wrhlearner/PacBot-2023/Docs/Hardware/components/motor driver/drv8835 schematic.png

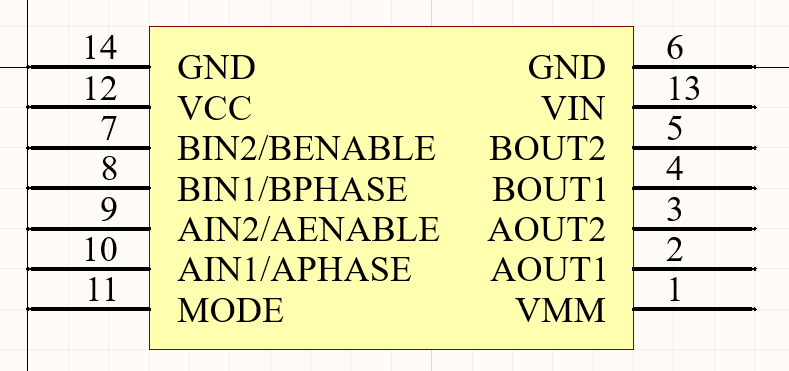
Docs/Hardware/components/motor driver/drv8835 schematic.png
