wrhlearner/PacBot-2023/Docs/Hardware/components/Teensy40/mechanical dimensions front side.png

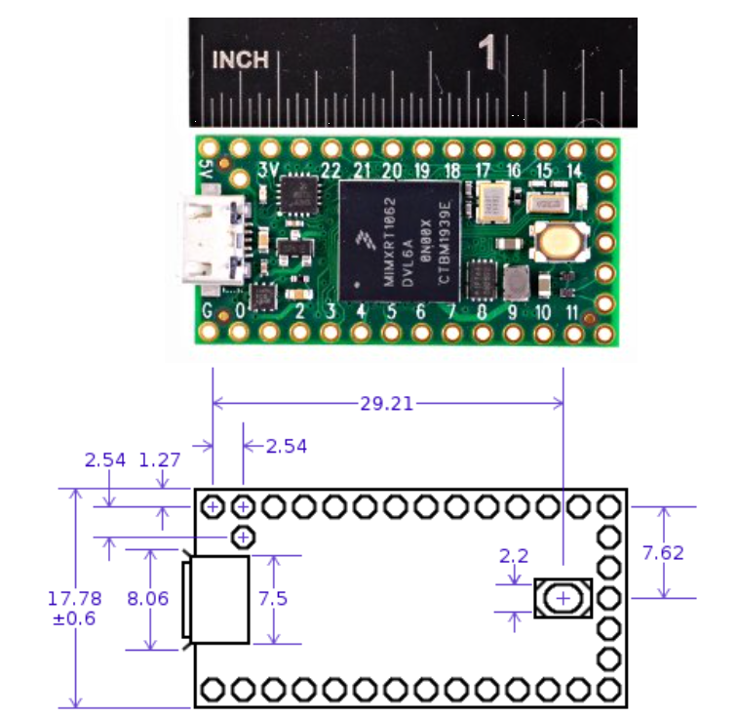
Docs/Hardware/components/Teensy40/mechanical dimensions front side.png
