wrhlearner/PacBot-2023/Docs/Hardware/PCB/3D model back.png

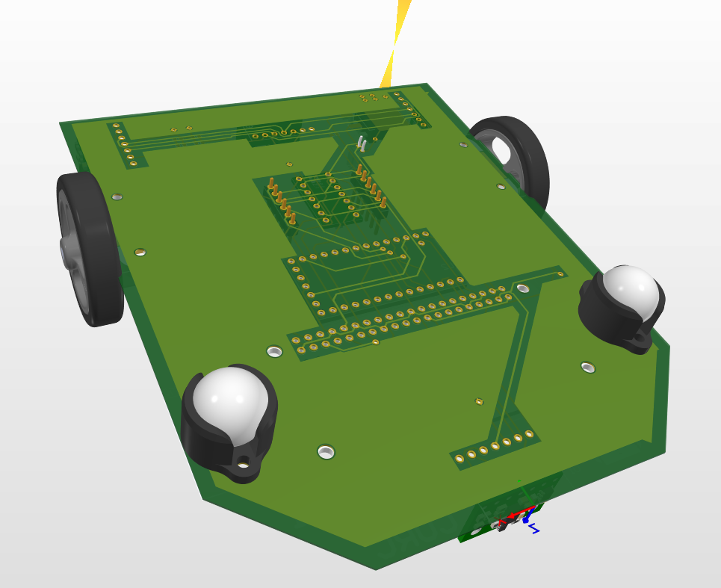
Docs/Hardware/PCB/3D model back.png
