wrhlearner/PacBot-2023/Docs/Hardware/components/magnetic encoder/PCB dimensions.jpg

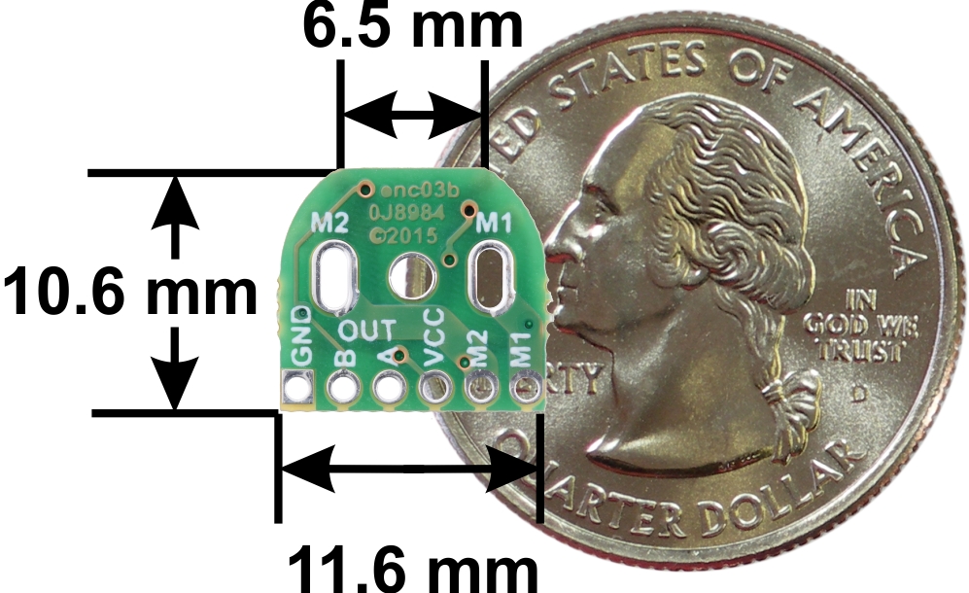
Docs/Hardware/components/magnetic encoder/PCB dimensions.jpg
