wrhlearner/PacBot-2023/Docs/Hardware/components/motor/mounting bracket back.jpg

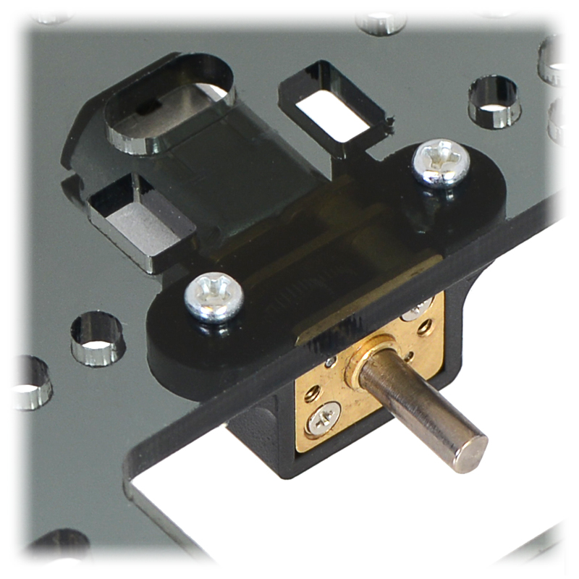
Docs/Hardware/components/motor/mounting bracket back.jpg
