wrhlearner/PacBot-2023/Docs/Hardware/components/Teensy40/Teensy_4.0/Teensy_4.0_PCB.SLDPRT

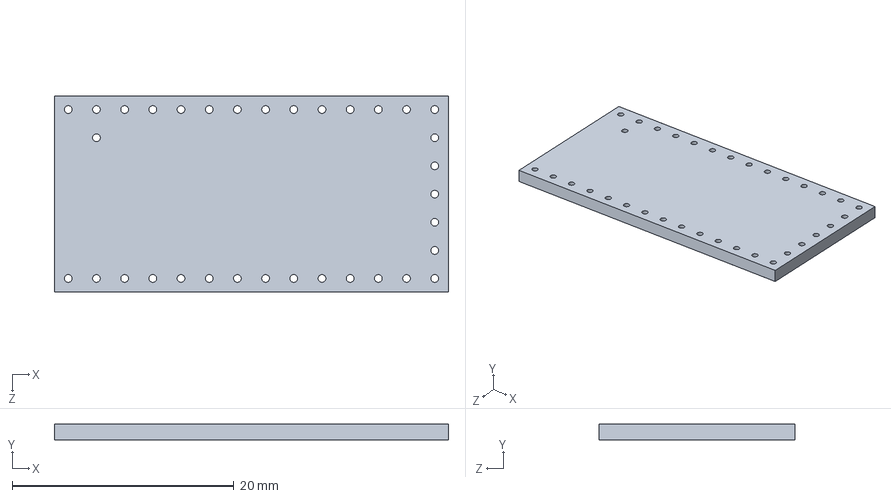
[picture p24: CAD file, 2023-03-19]
Docs/Hardware/components/Teensy40/Teensy_4.0/Teensy_4.0_PCB.SLDPRT
35.5 x 1.40 x 17.7 mm
