wrhlearner/PacBot-2023/Docs/Hardware/components/Teensy40/Teensy_4.0/SKRPACE010 v4.SLDPRT

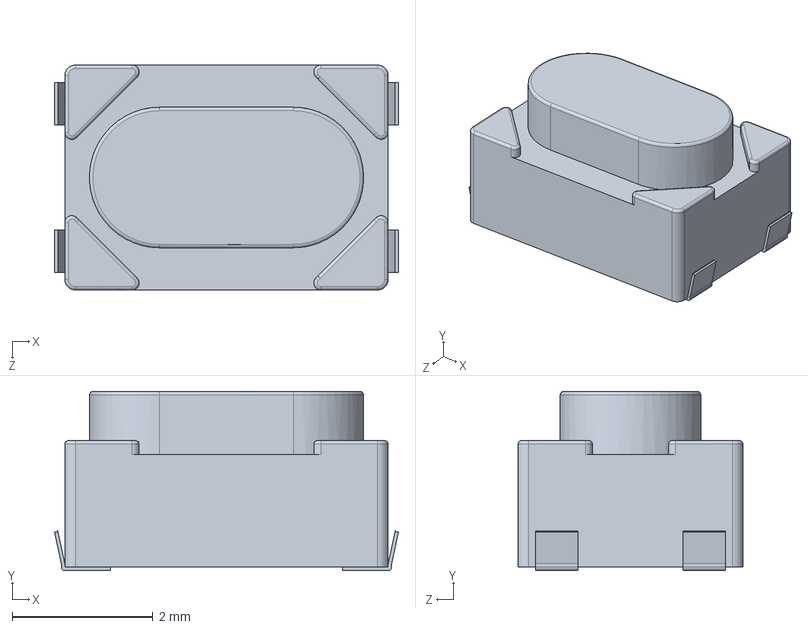
[picture p25: CAD file, 2023-03-19]
Docs/Hardware/components/Teensy40/Teensy_4.0/SKRPACE010 v4.SLDPRT
4.89 x 2.55 x 3.20 mm
