wrhlearner/PacBot-2023/Docs/Hardware/components/magnetic encoder/61300611121_Download_STP_61300611121_rev1.stp

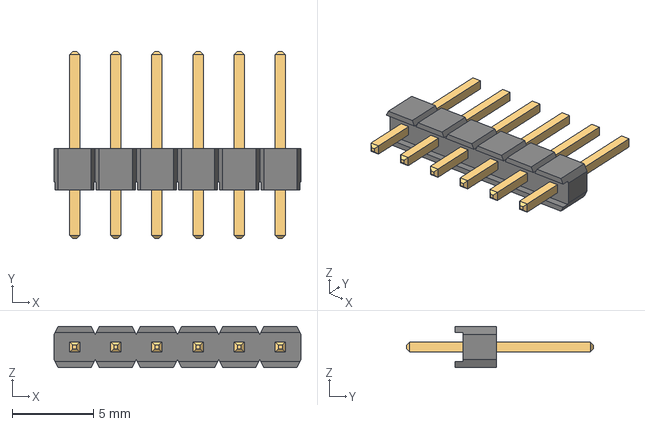
[picture p26: CAD file, 2023-03-19]
Docs/Hardware/components/magnetic encoder/61300611121_Download_STP_61300611121_rev1.stp
15.2 x 11.5 x 2.54 mm
6130xx11121_PIN x 6
