wrhlearner/PacBot-2023/Docs/Hardware/components/magnetic encoder/soldering 0.1'' male headers.jpg

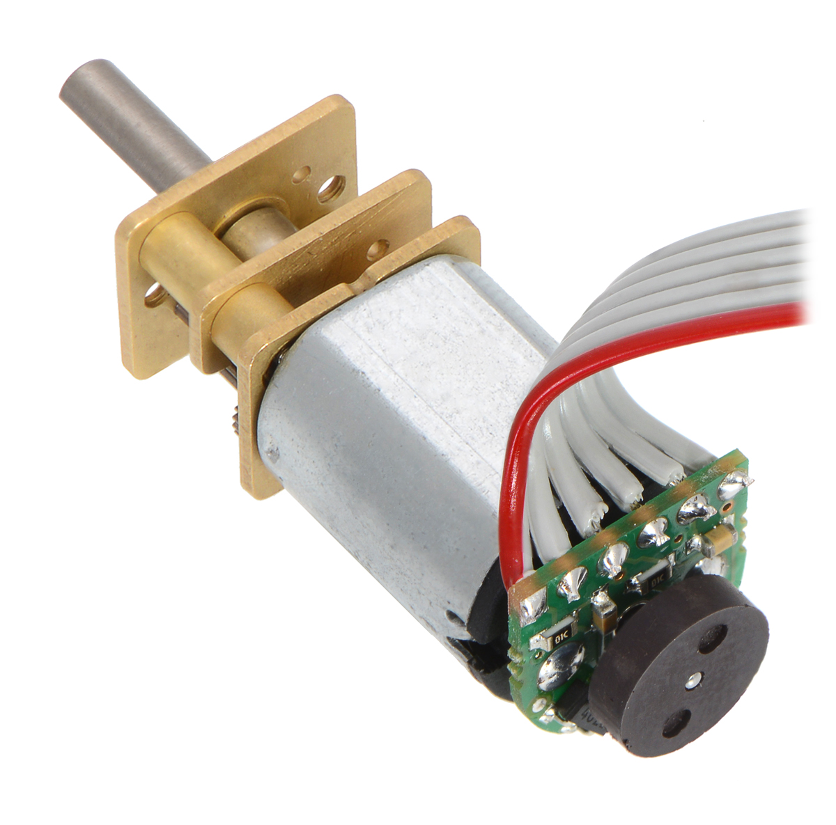
Docs/Hardware/components/magnetic encoder/soldering 0.1'' male headers.jpg
