wrhlearner/PacBot-2023/Docs/Hardware/components/RPY/2x20 GPIO header.pdf

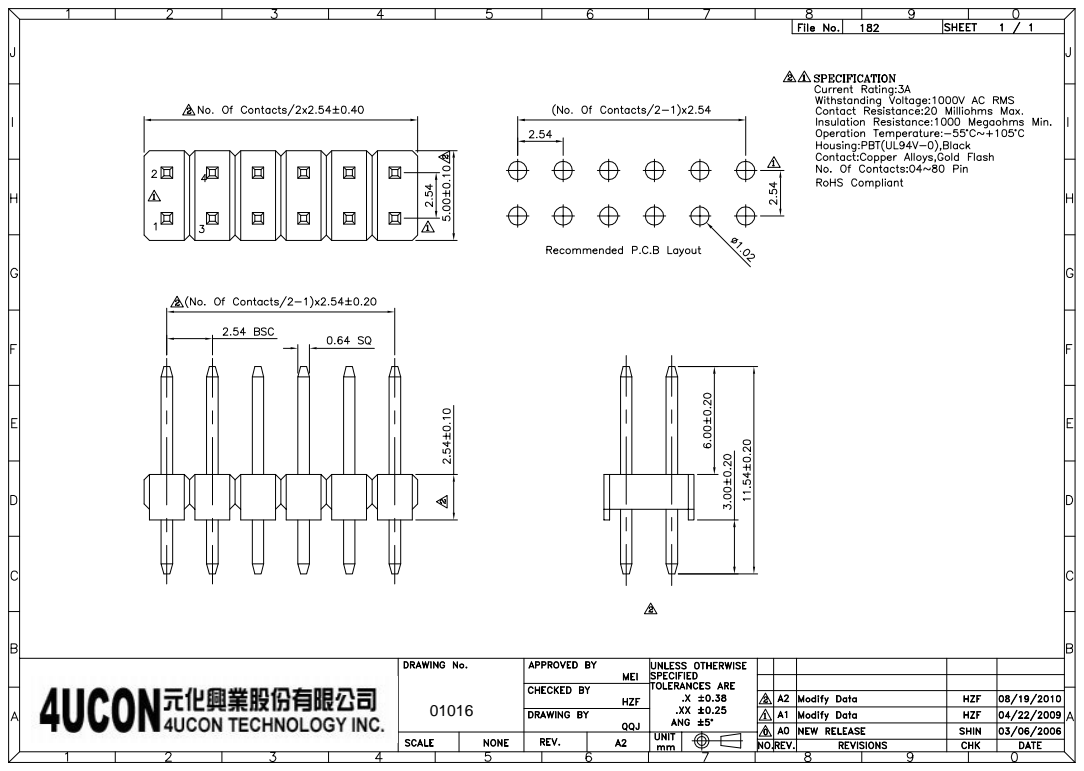
[picture p31: page 1]
