wrhlearner/PacBot-2023/Docs/Hardware/components/RPY/C4114.CP25412-40G-S116-A.pdf

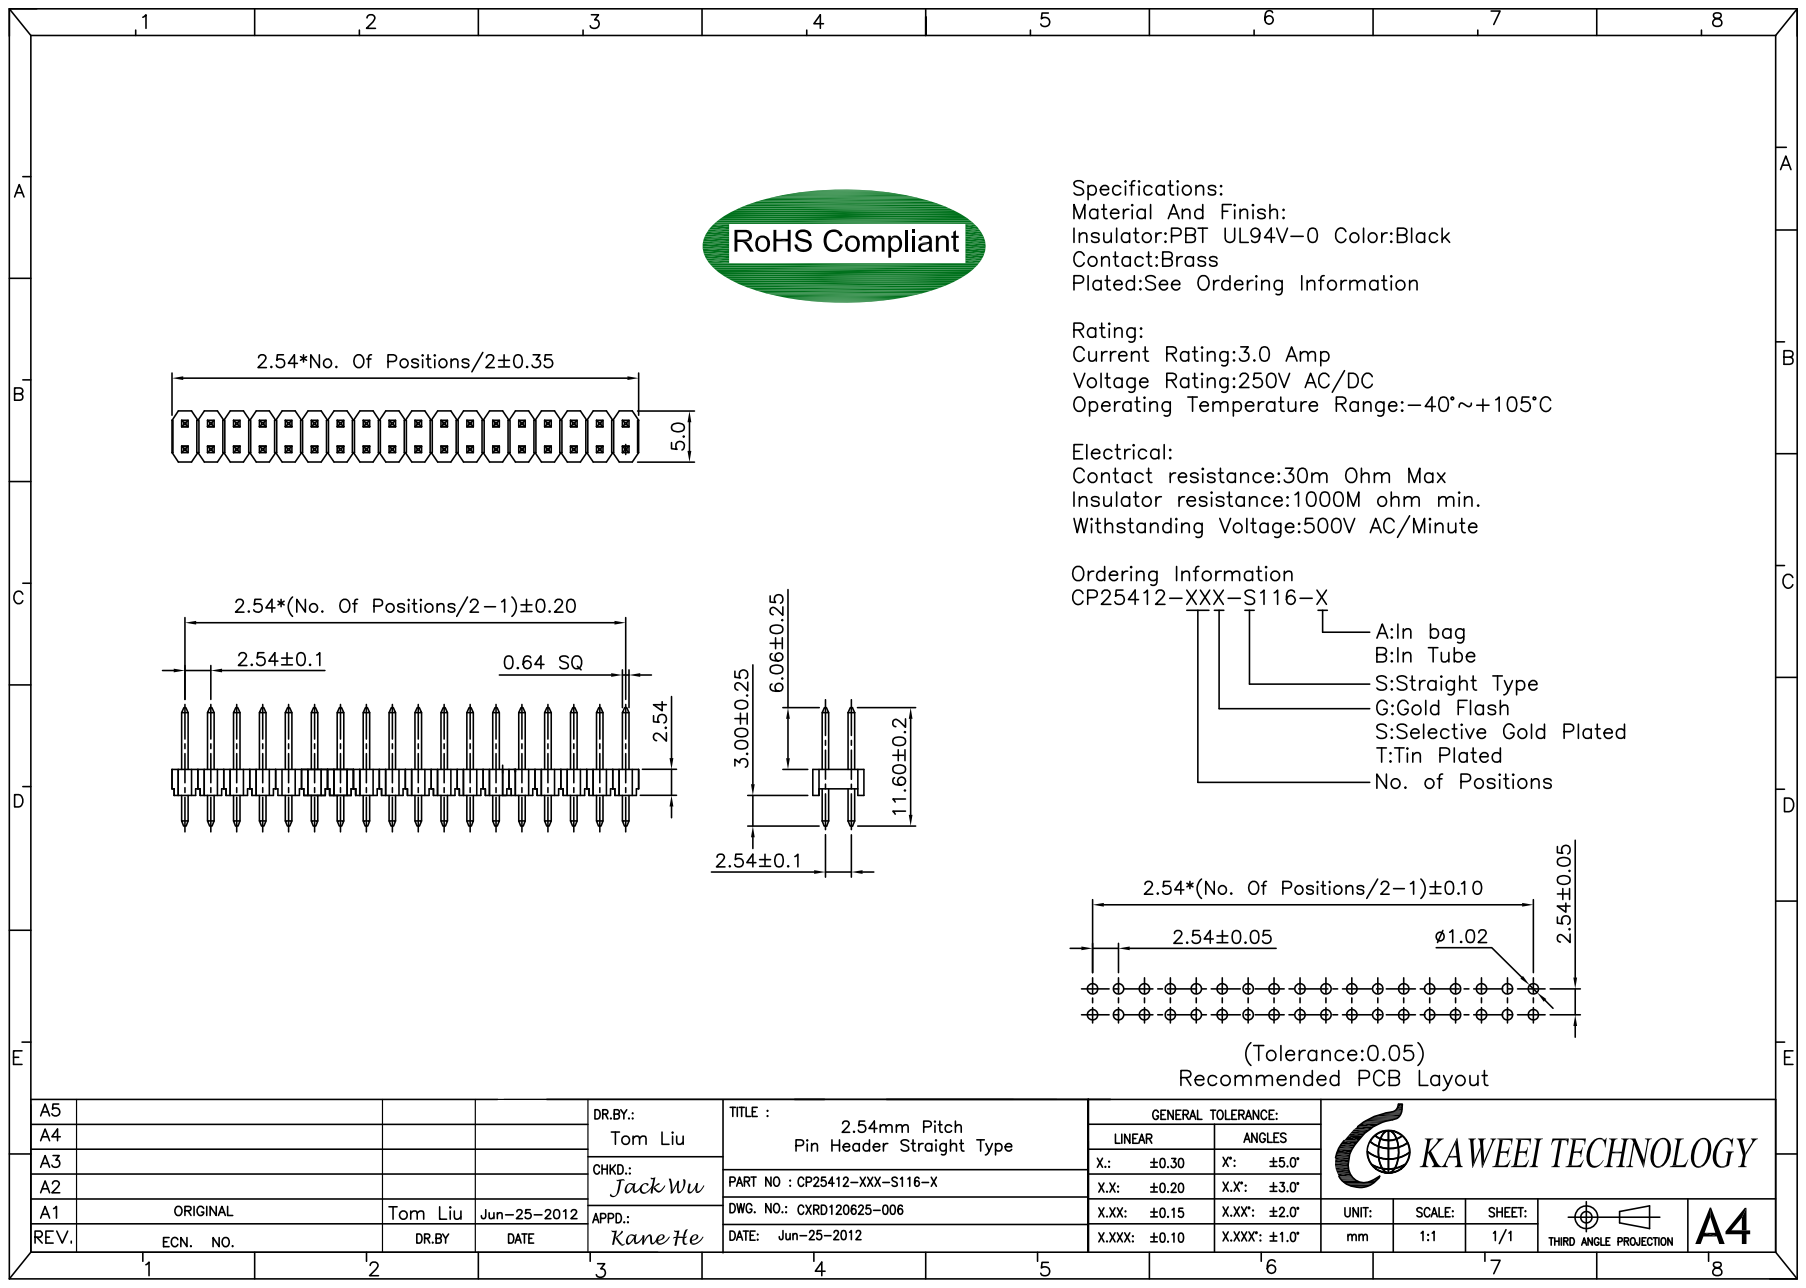
[picture p32: page 1]
